BenLBurke/touch_point/touchpoint/effects.py

"""LED ring animations.

Every function takes a `pixels`-like object -- anything that supports
``len()``, item assignment, ``fill()`` and ``show()`` (a real
``neopixel.NeoPixel``, or a plain list-based fake in tests) -- so the
animation logic can be exercised without any LED hardware attached.
"""
import random
import time

Color = tuple

FIREWORK_COLORS = [
    (255, 0, 0),      # red
    (255, 140, 0),    # orange
    (255, 255, 0),    # yellow
    (255, 255, 255),  # white
    (0, 0, 255),      # blue
    (128, 0, 128),    # purple
    (75, 0, 130),     # indigo
    (255, 20, 147),   # pink
]


def clear_pixels(pixels) -> None:
    pixels.fill((0, 0, 0))
    pixels.show()


def wheel(pos: int) -> Color:
    """Generate rainbow colors across 0-255 positions."""
    pos = pos % 256
    if pos < 85:
        return (255 - pos * 3, pos * 3, 0)
    if pos < 170:
        pos -= 85
        return (0, 255 - pos * 3, pos * 3)
    pos -= 170
    return (pos * 3, 0, 255 - pos * 3)


def comet(pixels, color: Color, tail_length: int = 12, delay: float = 0.03) -> None:
    n = len(pixels)
    for i in range(n + tail_length):
        pixels.fill((0, 0, 0))
        for j in range(tail_length):
            idx = (i - j) % n
            brightness = (tail_length - j) / tail_length
            pixels[idx] = tuple(int(c * brightness) for c in color)
        pixels.show()
        time.sleep(delay)


def burst(pixels) -> None:
    n = len(pixels)
    for _ in range(3):
        idx = random.randint(0, n - 1)
        color = random.choice(FIREWORK_COLORS)
        pixels[idx] = color
        pixels.show()
        time.sleep(0.05)
        pixels[idx] = (0, 0, 0)
        pixels.show()


def rainbow_cycle(pixels, duration: float = 1.0) -> None:
    n = len(pixels)
    steps = 60
    for i in range(steps):
        for j in range(n):
            rc_index = (j * 256 // n + i * 5) % 256
            pixels[j] = wheel(rc_index)
        pixels.show()
        time.sleep(duration / steps)


def fade_to_color(pixels, color: Color, duration: float = 3.0) -> None:
    steps = 30
    for i in range(steps):
        level = i / steps
        pixels.fill(tuple(int(c * level) for c in color))
        pixels.show()
        time.sleep(duration / steps)
    # Guarantee we land exactly on the target color instead of stopping
    # one step short of it.
    pixels.fill(color)
    pixels.show()


def fade_burst(pixels, pixel_index: int, color: Color, duration: float = 0.5, steps: int = 15) -> None:
    for i in range(steps):
        brightness = 1 - (i / steps)
        pixels[pixel_index] = tuple(int(c * brightness) for c in color)
        pixels.show()
        time.sleep(duration / steps)
    pixels[pixel_index] = (0, 0, 0)
    pixels.show()


def fireworks(pixels, num_bursts: int = 10, delay_between: float = 0.2) -> None:
    n = len(pixels)
    for _ in range(num_bursts):
        pixel = random.randint(0, n - 1)
        color = random.choice(FIREWORK_COLORS)
        pixels[pixel] = color
        pixels.show()
        fade_burst(pixels, pixel, color)
        time.sleep(delay_between)
